leonos2000/air_quality_sensor/media/assembly.png

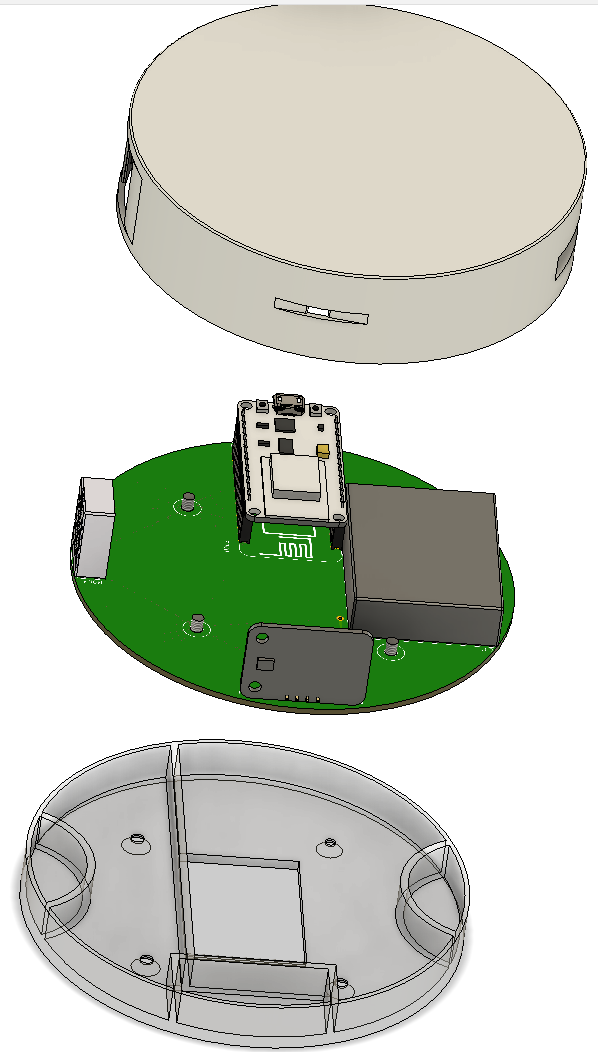
media/assembly.png
