leonos2000/air_quality_sensor/media/assembly_bottom.jpg

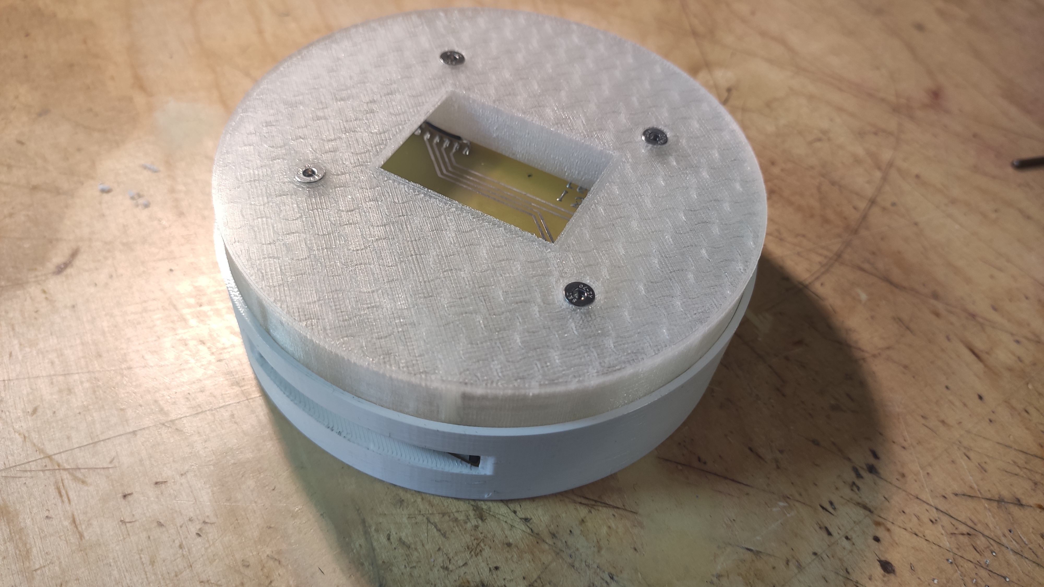
media/assembly_bottom.jpg
