leonos2000/air_quality_sensor/media/assembly_bottom_3d.png

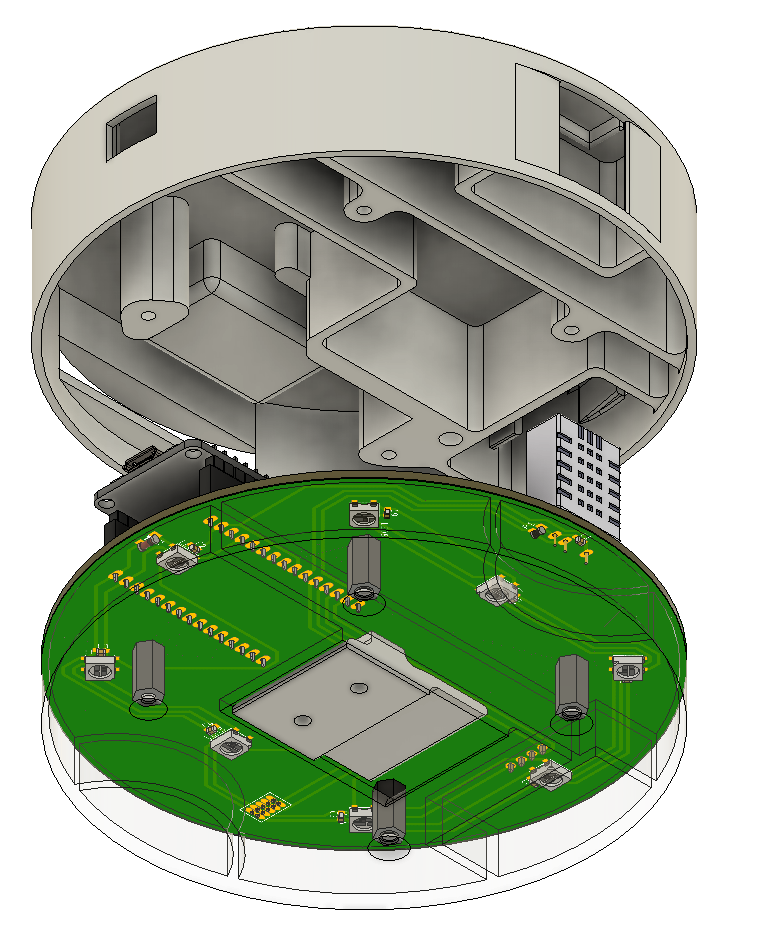
media/assembly_bottom_3d.png
